DF4IAH/avr_DF4IAH_10MHz_Bootloader/DF4IAH_10MHz_Bootloader_FW/DF4IAH_10MHz_Bootloader_FW/df4iah_bl_clkPullPwm.h

/*
 * df4iah_bl_clkPullPwm.h
 *
 *  Created on: 24.11.2014
 *      Author: espero
 */

#ifndef DF4IAH_BL_CLKPULLPWM_H_
#define DF4IAH_BL_CLKPULLPWM_H_


#define DEFAULT_PWM_COUNT  									120


void clkPullPwm_bl_init();
void clkPullPwm_bl_close();

void clkPullPwm_bl_togglePin();
void clkPullPwm_bl_endlessTogglePin();

#endif /* DF4IAH_BL_CLKPULLPWM_H_ */
